JiannnH/MTL-BaroTactileSensor/Data_collection/tip1/test0710_20230710_153429.csv

Sensor_0 | Sensor_1 | Sensor_2 | Sensor_3 | x | z | time
101356.75 | 101346.50 | 101364.75 | 101401.75 | 0 | 0 | 0.0
101332.50 | 101330.00 | 101333.25 | 101376.25 | 0 | 0 | 0.015215635299682617
101341.50 | 101338.25 | 101345.50 | 101381.00 | 0 | 0 | 0.03066849708557129
101347.00 | 101340.50 | 101357.00 | 101377.25 | 0 | 0 | 0.04594016075134277
101348.75 | 101339.25 | 101356.00 | 101385.75 | 0 | 0 | 0.06135392189025879
101353.50 | 101343.00 | 101353.25 | 101396.75 | 0 | 0 | 0.0780799388885498
101354.25 | 101332.50 | 101355.25 | 101388.75 | 0 | 0 | 0.09276247024536133
101348.00 | 101342.50 | 101359.50 | 101408.75 | 0 | 0 | 0.10820293426513672
101357.25 | 101344.00 | 101363.75 | 101386.00 | 0 | 0 | 0.12340831756591797
101358.75 | 101356.00 | 101358.00 | 101390.50 | 0 | 0 | 0.13866806030273438
101363.50 | 101353.25 | 101354.00 | 101394.25 | 0 | 0 | 0.15439748764038086
101359.00 | 101351.25 | 101355.75 | 101402.50 | 0 | 0 | 0.16908740997314453
101361.25 | 101349.50 | 101363.50 | 101407.00 | 0 | 0 | 0.18455219268798828
101363.25 | 101354.50 | 101360.00 | 101389.00 | 0 | 0 | 0.1989912986755371
101364.00 | 101346.50 | 101355.50 | 101404.00 | 0 | 0 | 0.21437811851501465
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
