JiannnH/MTL-BaroTactileSensor/Data_collection/tip1/test0710_20230710_153756.csv

Sensor_3_new | Sensor_3 | Sensor_3_new | Sensor_3
101362.75 | 101381.25 | 0.000177007 | -0.012790445
101341.75 | 101342 | -0.000673405 | -0.142960865
101334.5 | 101360.75 | -0.000984008 | -0.085370001
101340 | 101369.5 | -0.00077696 | -0.059032682
101351.25 | 101379.5 | -0.000336721 | -0.027914694
101354.25 | 101387.5 | -0.000221042 | -0.002467206
101355.75 | 101390.75 | -0.000176411 | 0.007699641
101360.5 | 101382.5 | 1.70035E-05 | -0.01867995
101364.5 | 101394.75 | 0.000175502 | 0.021092509
101356.75 | 101390 | -0.00013451 | 0.005595328
101362 | 101390.75 | 9.04821E-05 | 0.008378319
101355 | 101373.75 | -0.000185516 | -0.047788821
101365.25 | 101392.25 | 0.000235615 | 0.009975735
101357.75 | 101380.25 | -6.5583E-05 | -0.030353553
101363.5 | 101378.25 | 0.000173977 | -0.041516868
101372.25 | 101391.25 | 0.000540752 | -0.000740777
101355.75 | 101385.5 | -0.000122358 | -0.021134594
101359.5 | 101387.75 | 2.9451E-05 | -0.013169924
101348.75 | 101392 | -0.000417173 | 0.000889724
101359.75 | 101387.5 | 3.21838E-05 | -0.014085203
101358.25 | 101383.5 | -2.15569E-05 | -0.027248697
101361.75 | 101384.25 | 0.000121447 | -0.025108739
101360.5 | 101391.75 | 6.16351E-05 | -0.00049456
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
