JiannnH/MTL-BaroTactileSensor/Data_collection/tip1/test0710_20230710_153922.csv

Sensor_0 | Sensor_1 | Sensor_2 | Sensor_3 | x | z | time
101341.00 | 101323.75 | 101338.50 | 101359.25 | 0 | 0 | 0.0
101299.25 | 101296.75 | 101313.50 | 101340.00 | 0 | 0 | 0.01610422134399414
101313.75 | 101309.75 | 101326.75 | 101347.50 | 0 | 0 | 0.03152322769165039
101318.00 | 101313.50 | 101338.00 | 101360.25 | 0 | 0 | 0.0473482608795166
101321.25 | 101316.00 | 101332.25 | 101371.00 | 0 | 0 | 0.06226634979248047
101327.00 | 101318.25 | 101331.75 | 101379.25 | 0 | 0 | 0.07785320281982422
101331.00 | 101315.50 | 101340.25 | 101369.50 | 0 | 0 | 0.09486579895019531
101321.50 | 101323.75 | 101336.50 | 101371.25 | 0 | 0 | 0.10814166069030762
101333.00 | 101325.25 | 101337.00 | 101378.00 | 0 | 0 | 0.12410950660705566
101340.75 | 101325.75 | 101345.00 | 101367.50 | 0 | 0 | 0.14044809341430664
101334.00 | 101327.50 | 101330.50 | 101379.00 | 0 | 0 | 0.1554872989654541
101327.25 | 101323.75 | 101344.75 | 101375.50 | 0 | 0 | 0.1707291603088379
101327.00 | 101338.25 | 101339.75 | 101365.50 | 0 | 0 | 0.1867692470550537
101330.25 | 101320.75 | 101340.75 | 101380.25 | 0 | 0 | 0.2029709815979004
101340.50 | 101316.75 | 101340.75 | 101377.50 | 0 | 0 | 0.21901988983154297
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
