JiannnH/MTL-BaroTactileSensor/Data_collection/tip1/test0710_20230710_154212.csv

Sensor_0 | Sensor_1 | Sensor_2 | Sensor_3 | x | z | time
101328.00 | 101326.00 | 101324.00 | 101362.75 | 0 | 0 | 0.0
101306.75 | 101301.00 | 101299.50 | 101341.75 | 0 | 0 | 0.016003131866455078
101295.75 | 101301.50 | 101302.75 | 101334.50 | 0 | 0 | 0.031578779220581055
101313.25 | 101307.25 | 101303.00 | 101340.00 | 0 | 0 | 0.04734325408935547
101320.50 | 101313.00 | 101313.75 | 101351.25 | 0 | 0 | 0.0642707347869873
101318.50 | 101329.00 | 101314.00 | 101354.25 | 0 | 0 | 0.07938838005065918
101314.25 | 101317.25 | 101317.25 | 101355.75 | 0 | 0 | 0.09466934204101562
101319.50 | 101321.00 | 101318.75 | 101360.50 | 0 | 0 | 0.10965466499328613
101321.75 | 101322.50 | 101315.75 | 101364.50 | 0 | 0 | 0.1262531280517578
101327.75 | 101316.00 | 101326.50 | 101356.75 | 0 | 0 | 0.13970589637756348
101326.75 | 101326.00 | 101315.50 | 101362.00 | 0 | 0 | 0.15646147727966309
101325.75 | 101316.00 | 101331.75 | 101355.00 | 0 | 0 | 0.17235231399536133
101323.00 | 101322.25 | 101325.50 | 101365.25 | 0 | 0 | 0.1878352165222168
101330.50 | 101322.50 | 101312.75 | 101357.75 | 0 | 0 | 0.20330166816711426
101324.50 | 101317.75 | 101331.75 | 101363.50 | 0 | 0 | 0.21893739700317383
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
