JiannnH/MTL-BaroTactileSensor/Data_collection/tip1/test_20230703_122221.csv

Sensor_0 | Sensor_1 | Sensor_2 | Sensor_3 | x | z | time
96400.50 | 100019.50 | 97869.50 | 111716.50 | 0 | 0 | 0.0
96352.75 | 99946.50 | 97830.25 | 111645.00 | 0 | 0 | 0.014998912811279297
96369.00 | 99940.00 | 97829.50 | 111653.00 | 0 | 0 | 0.029145240783691406
96370.25 | 99956.25 | 97844.50 | 111662.50 | 0 | 0 | 0.045772552490234375
96377.25 | 99972.00 | 97850.50 | 111673.00 | 0 | 0 | 0.062323570251464844
96378.75 | 99979.25 | 97847.75 | 111669.75 | 0 | 0 | 0.07733964920043945
96393.50 | 99972.00 | 97845.50 | 111683.50 | 0 | 0 | 0.09400701522827148
96390.25 | 99978.75 | 97846.50 | 111679.00 | 0 | 0 | 0.10734009742736816
96394.50 | 99993.00 | 97856.25 | 111691.25 | 0 | 0 | 0.1223595142364502
96389.25 | 99984.75 | 97855.00 | 111695.25 | 0 | 0 | 0.1390080451965332
96385.25 | 99987.25 | 97859.00 | 111694.00 | 0 | 0 | 0.15428638458251953
96392.75 | 99991.00 | 97849.00 | 111701.00 | 0 | 0 | 0.16861343383789062
96405.50 | 99995.50 | 97857.25 | 111684.75 | 0 | 0 | 0.18474173545837402
96401.50 | 99999.00 | 97862.50 | 111698.25 | 0 | 0 | 0.20013022422790527
96392.50 | 99996.00 | 97863.75 | 111703.75 | 0 | 0 | 0.21539688110351562
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
